RICCIARDI-Adrien/Christmas_Tree/Software/Sources/PWM.c

/** @file PWM.c
 * See PWM.h for description.
 * @author Adrien RICCIARDI
 */
#include <PWM.h>
#include <xc.h>

//-------------------------------------------------------------------------------------------------
// Private types
//-------------------------------------------------------------------------------------------------
/** Access table to reach a PWM channel registers as fast as possible. */
typedef struct
{
	volatile unsigned char *Pointer_Duty_Cycle_High_Register; //!< Store duty cycle period bits 9..2.
	volatile unsigned char *Pointer_Duty_Cycle_Low_Register; //!< Store duty cycle period bits 2..0 in register bits 5..4.
} TPWMChannel;

//-------------------------------------------------------------------------------------------------
// Private variables
//-------------------------------------------------------------------------------------------------
/** All PWM channels. */
static TPWMChannel PWM_Channels[PWM_CHANNEL_IDS_COUNT] =
{
	// PWM_CHANNEL_ID_STAR
	{
		&CCPR1L,
		&CCP1CON
	},
	// PWM_CHANNEL_ID_RED_FAIRY_LIGHTS
	{
		&CCPR2L,
		&CCP2CON
	},
	// PWM_CHANNEL_ID_BLUE_FAIRY_LIGHTS
	{
		&CCPR3L,
		&CCP3CON
	},
	// PWM_CHANNEL_ID_YELLOW_FAIRY_LIGHTS
	{
		&CCPR5L,
		&CCP5CON
	}
};

//-------------------------------------------------------------------------------------------------
// Public functions
//-------------------------------------------------------------------------------------------------
void PWMInitialize(void)
{
	// Configure CCP1 PWM as a single PWM (it's an enhanced full-bridge one)
	CCP1CON = 0x0C; // Enable single output mode, select PWM mode
	ECCP1AS = 0; // Disable auto-shutdown feature
	
	// Configure CCP2 PWM as a single PWM (it's an enhanced half-bridge one)
	CCP2CON = 0x0C; // Enable single output mode, select PWM mode
	ECCP2AS = 0; // Disable auto-shutdown feature
	
	// Configure CCP3 PWM as a single PWM (it's an enhanced half-bridge one)
	CCP3CON = 0x0C; // Enable single output mode, select PWM mode
	ECCP3AS = 0; // Disable auto-shutdown feature
	
	// Configure CCP5 PWM (it's standard one)
	CCP5CON = 0x0C; // Select PWM mode
	
	// Use timer 2 to clock all PWM modules
	CCPTMRS0 = 0; // Select timer 2 as clock source for CCP1, CCP2 and CCP3
	CCPTMRS1 = 0; // Select timer 2 as clock source for CCP5
	
	// Configure timer 2 to generate a PWM period of about 244Hz
	TMR2 = 0;
	PR2 = 255; // Divide oscillator clock by 4 (timer clock input), then by 16 (prescaler), then by 256 (this register value)
	T2CON = 0x06; // Select no postscaler as it is not used in PWM mode, select 1:16 prescaler, enable timer
	
	// Configure all channels pins now that PWM are operational
	// Turn all leds off on boot
	LATA = 0;
	LATB = 0;
	LATC = 0;
	// Set all ports pins as digital
	ANSELA = 0;
	ANSELB = 0;
	ANSELC = 0;
	// Set all ports pins as output
	TRISA = 0;
	TRISB = 0;
	TRISC = 0;
}

void PWMSetDutyCycle(TPWMChannelID Channel_ID, unsigned short Duty_Cycle_Period)
{
	TPWMChannel *Pointer_Channel;
	
	// Cache channel access
	Pointer_Channel = &PWM_Channels[Channel_ID];
	
	// Set least significant bits
	*(Pointer_Channel->Pointer_Duty_Cycle_Low_Register) &= 0xCF; // Clear bits 5..4
	*(Pointer_Channel->Pointer_Duty_Cycle_Low_Register) |= (Duty_Cycle_Period << 4) & 0x30;
	
	// Set most significant bits
	*(Pointer_Channel->Pointer_Duty_Cycle_High_Register) = Duty_Cycle_Period >> 2;
}
